dmsmccann/triton-540/spice/studies/80279/closed-loop-agc/figures/80279-full-rf-agc-attack.png

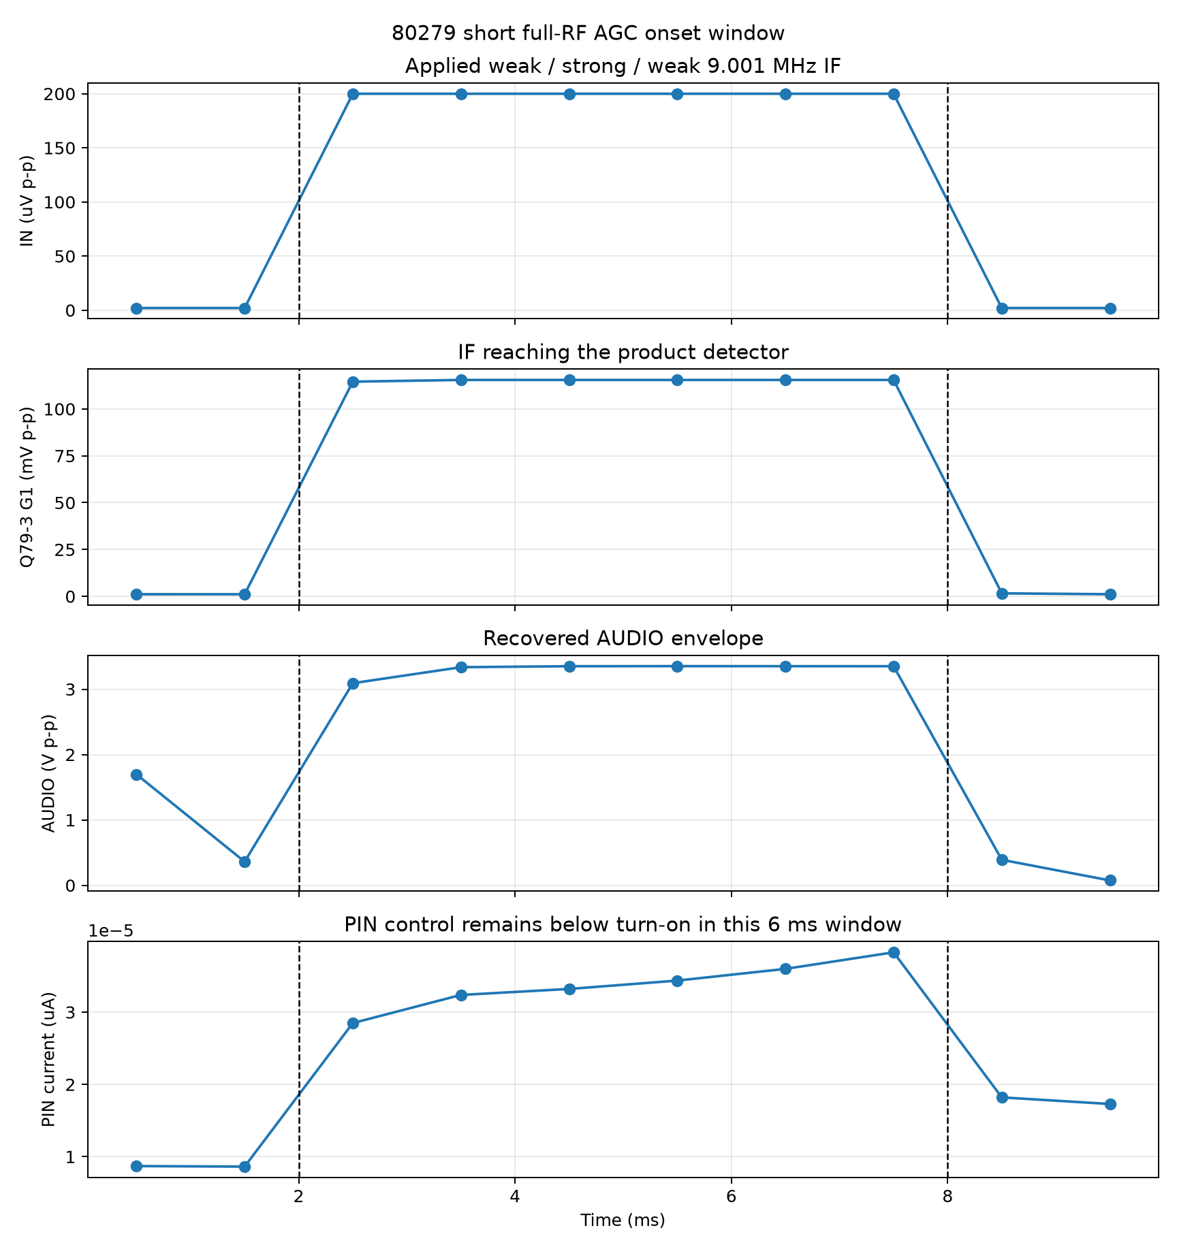
spice/studies/80279/closed-loop-agc/figures/80279-full-rf-agc-attack.png
