dmsmccann/triton-540/spice/studies/80166/manual-alignment/data/final/29p0_saved-schematic-validation.csv

frequency | user0 (gain) | user3 (gain)
28970000.0 | 71.26063842635646 | 39.748845762307894
28970444.70934756 | 71.27956110949187 | 39.75944934947092
28970889.42552171 | 71.29823011865204 | 39.76979173254958
28971334.14852256 | 71.31664334363214 | 39.779870788589776
28971778.87835021 | 71.33479870270592 | 39.789684423269634
28972223.61500477 | 71.3526941439815 | 39.79923057171336
28972668.35848634 | 71.3703276625861 | 39.808507216010966
28973113.10879503 | 71.38769728793825 | 39.81751237291327
28973557.86593094 | 71.40480109264368 | 39.826244102123084
28974002.62989417 | 71.42163719953496 | 39.834700513735925
28974447.40068484 | 71.4382037585815 | 39.84287974439121
28974892.17830305 | 71.45449897340933 | 39.85077998491168
28975336.9627489 | 71.47052108866878 | 39.858399467109926
28975781.75402249 | 71.48626840090347 | 39.865736474129626
28976226.55212393 | 71.50173925256661 | 39.87278933568876
28976671.35705333 | 71.51693202979676 | 39.87955642448672
28977116.16881079 | 71.53184517581325 | 39.88603617075028
28977560.98739642 | 71.54647717821462 | 39.89222704893736
28978005.81281031 | 71.56082657508746 | 39.89812758428635
28978450.64505258 | 71.57489196675368 | 39.903736363170175
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
