dmsmccann/triton-540/spice/studies/80289/signal-walk/data/80289-vfo-80m-signal-walk-measurements.csv

trace | mean_v | minimum_v | maximum_v | peak_to_peak_v | dominant_frequency_hz | component_2.25mhz_vpp | component_5.25mhz_vpp | component_7.5mhz_vpp | component_12.75mhz_vpp
pto_emitter_v | 1.6999995103719476 | 1.400000068162442 | 1.999999931837529 | 0.599999863675087 | 5249737.513112833 | 1.9583204355397362e-06 | 0.5999999999999996 | 1.95836131415542e-06 | 1.9584461486022534e-06
crystal_q89_3_drain_v | 7.744778808784965 | 7.742017280589295 | 7.747588980160948 | 0.00557169957165371 | 7499625.018732619 | 2.097939089247529e-06 | 7.575498280821965e-07 | 0.005557396366243375 | 6.504599511085788e-07
u89_1_pin1_v | 6.787216149807024 | 6.659375419694097 | 6.914867084712115 | 0.2554916650180177 | 5249737.513112833 | 2.480746723781994e-05 | 0.2552959477927164 | 4.365470808401273e-05 | 1.3487083771736018e-05
u89_1_pin4_v | 6.783145997120302 | 6.782941030756546 | 6.783341226276571 | 0.00040019552002501513 | 7499625.018732619 | 6.6934227813603936e-06 | 0.0001793814597817073 | 0.0002103364941931809 | 3.960542510357234e-07
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
