dmsmccann/triton-540/80166_rf_amp.kicad_sch

## KiCad design 80166_rf_amp.kicad_sch (2026-08-30, an earlier design)

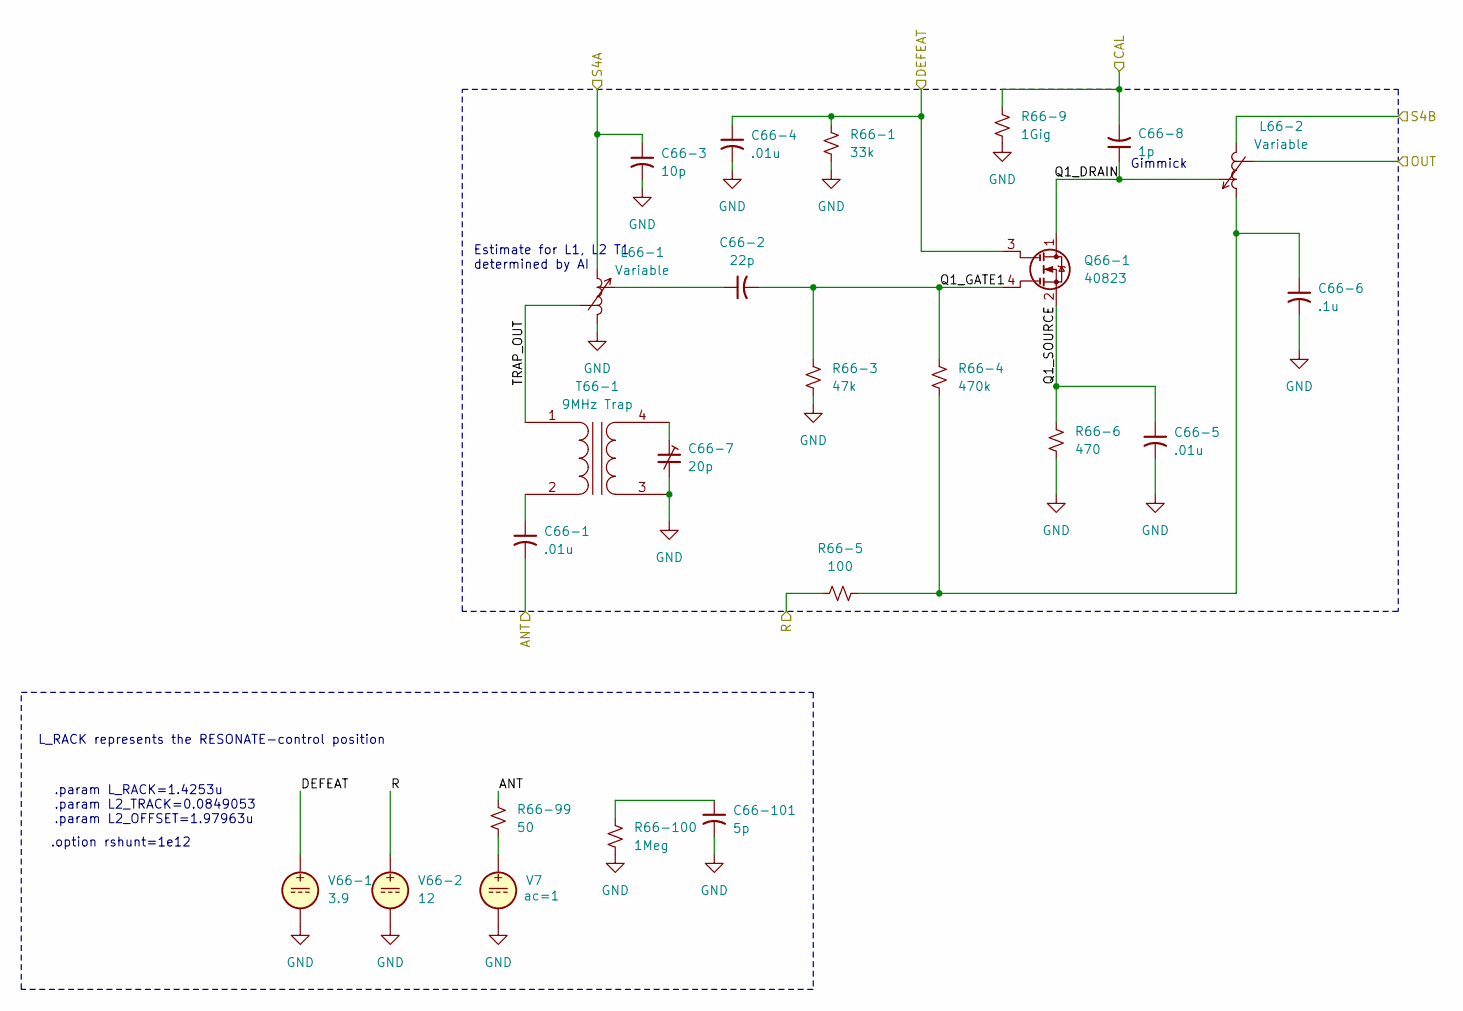
[picture p42: schematic 80166_rf_amp.kicad_sch]

Parts:
C66-1, C66-4, C66-5: .01u
C66-2: 22p
C66-3: 10p
C66-6: .1u
C66-7: 20p
C66-8: 1p
C66-101: 5p
L66-1, L66-2: Variable
Q66-1: 40823; TO-72-4
R66-1: 33k
R66-3: 47k
R66-4: 470k
R66-5: 100
R66-6: 470
R66-9: 1Gig
R66-99: 50
R66-100: 1Meg
T66-1: 9MHz Trap
V7: 0
V66-1: 3.9
V66-2: 12

Connections:
ANT: C66-1.2, R66-99.2
CAL: C66-8.2, R66-9.2
DEFEAT: C66-4.1, Q66-1.3 (G1), R66-1.2, V66-1.1
GND: C66-3.2, C66-4.2, C66-5.2, C66-6.2, C66-7.2, C66-101.2, L66-1.2, R66-1.1, R66-3.1, R66-6.1, R66-9.1, R66-100.1, T66-1.3 (SA), V7.2, V66-1.2, V66-2.2
unnamed: C66-1.1, T66-1.2 (AB)
unnamed: C66-2.1, L66-1.4
unnamed: C66-6.1, L66-2.1, R66-4.1, R66-5.2
unnamed: C66-7.1, T66-1.4 (SB)
unnamed: C66-101.1, R66-100.2
unnamed: R66-99.1, V7.1
OUT: L66-2.3
Q1_DRAIN: C66-8.1, L66-2.4, Q66-1.1 (D)
Q1_GATE1: C66-2.2, Q66-1.4 (S), R66-3.2, R66-4.2
Q1_SOURCE: C66-5.1, Q66-1.2 (G2), R66-6.2
R: R66-5.1, V66-2.1
S4A: C66-3.1, L66-1.1
S4B: L66-2.2
TRAP_OUT: L66-1.3, T66-1.1 (AA)

Notes on the sheet:
.param L_RACK=1.4253u .param L2_TRACK=0.0849053 .param L2_OFFSET=1.97963u
Gimmick
L_RACK represents the RESONATE-control position
.option rshunt=1e12
Estimate for L1, L2 T1 determined by AI
