dmsmccann/triton-540/80274_audio_power_amp.kicad_sch

## KiCad design 80274_audio_power_amp.kicad_sch (2026-09-05)

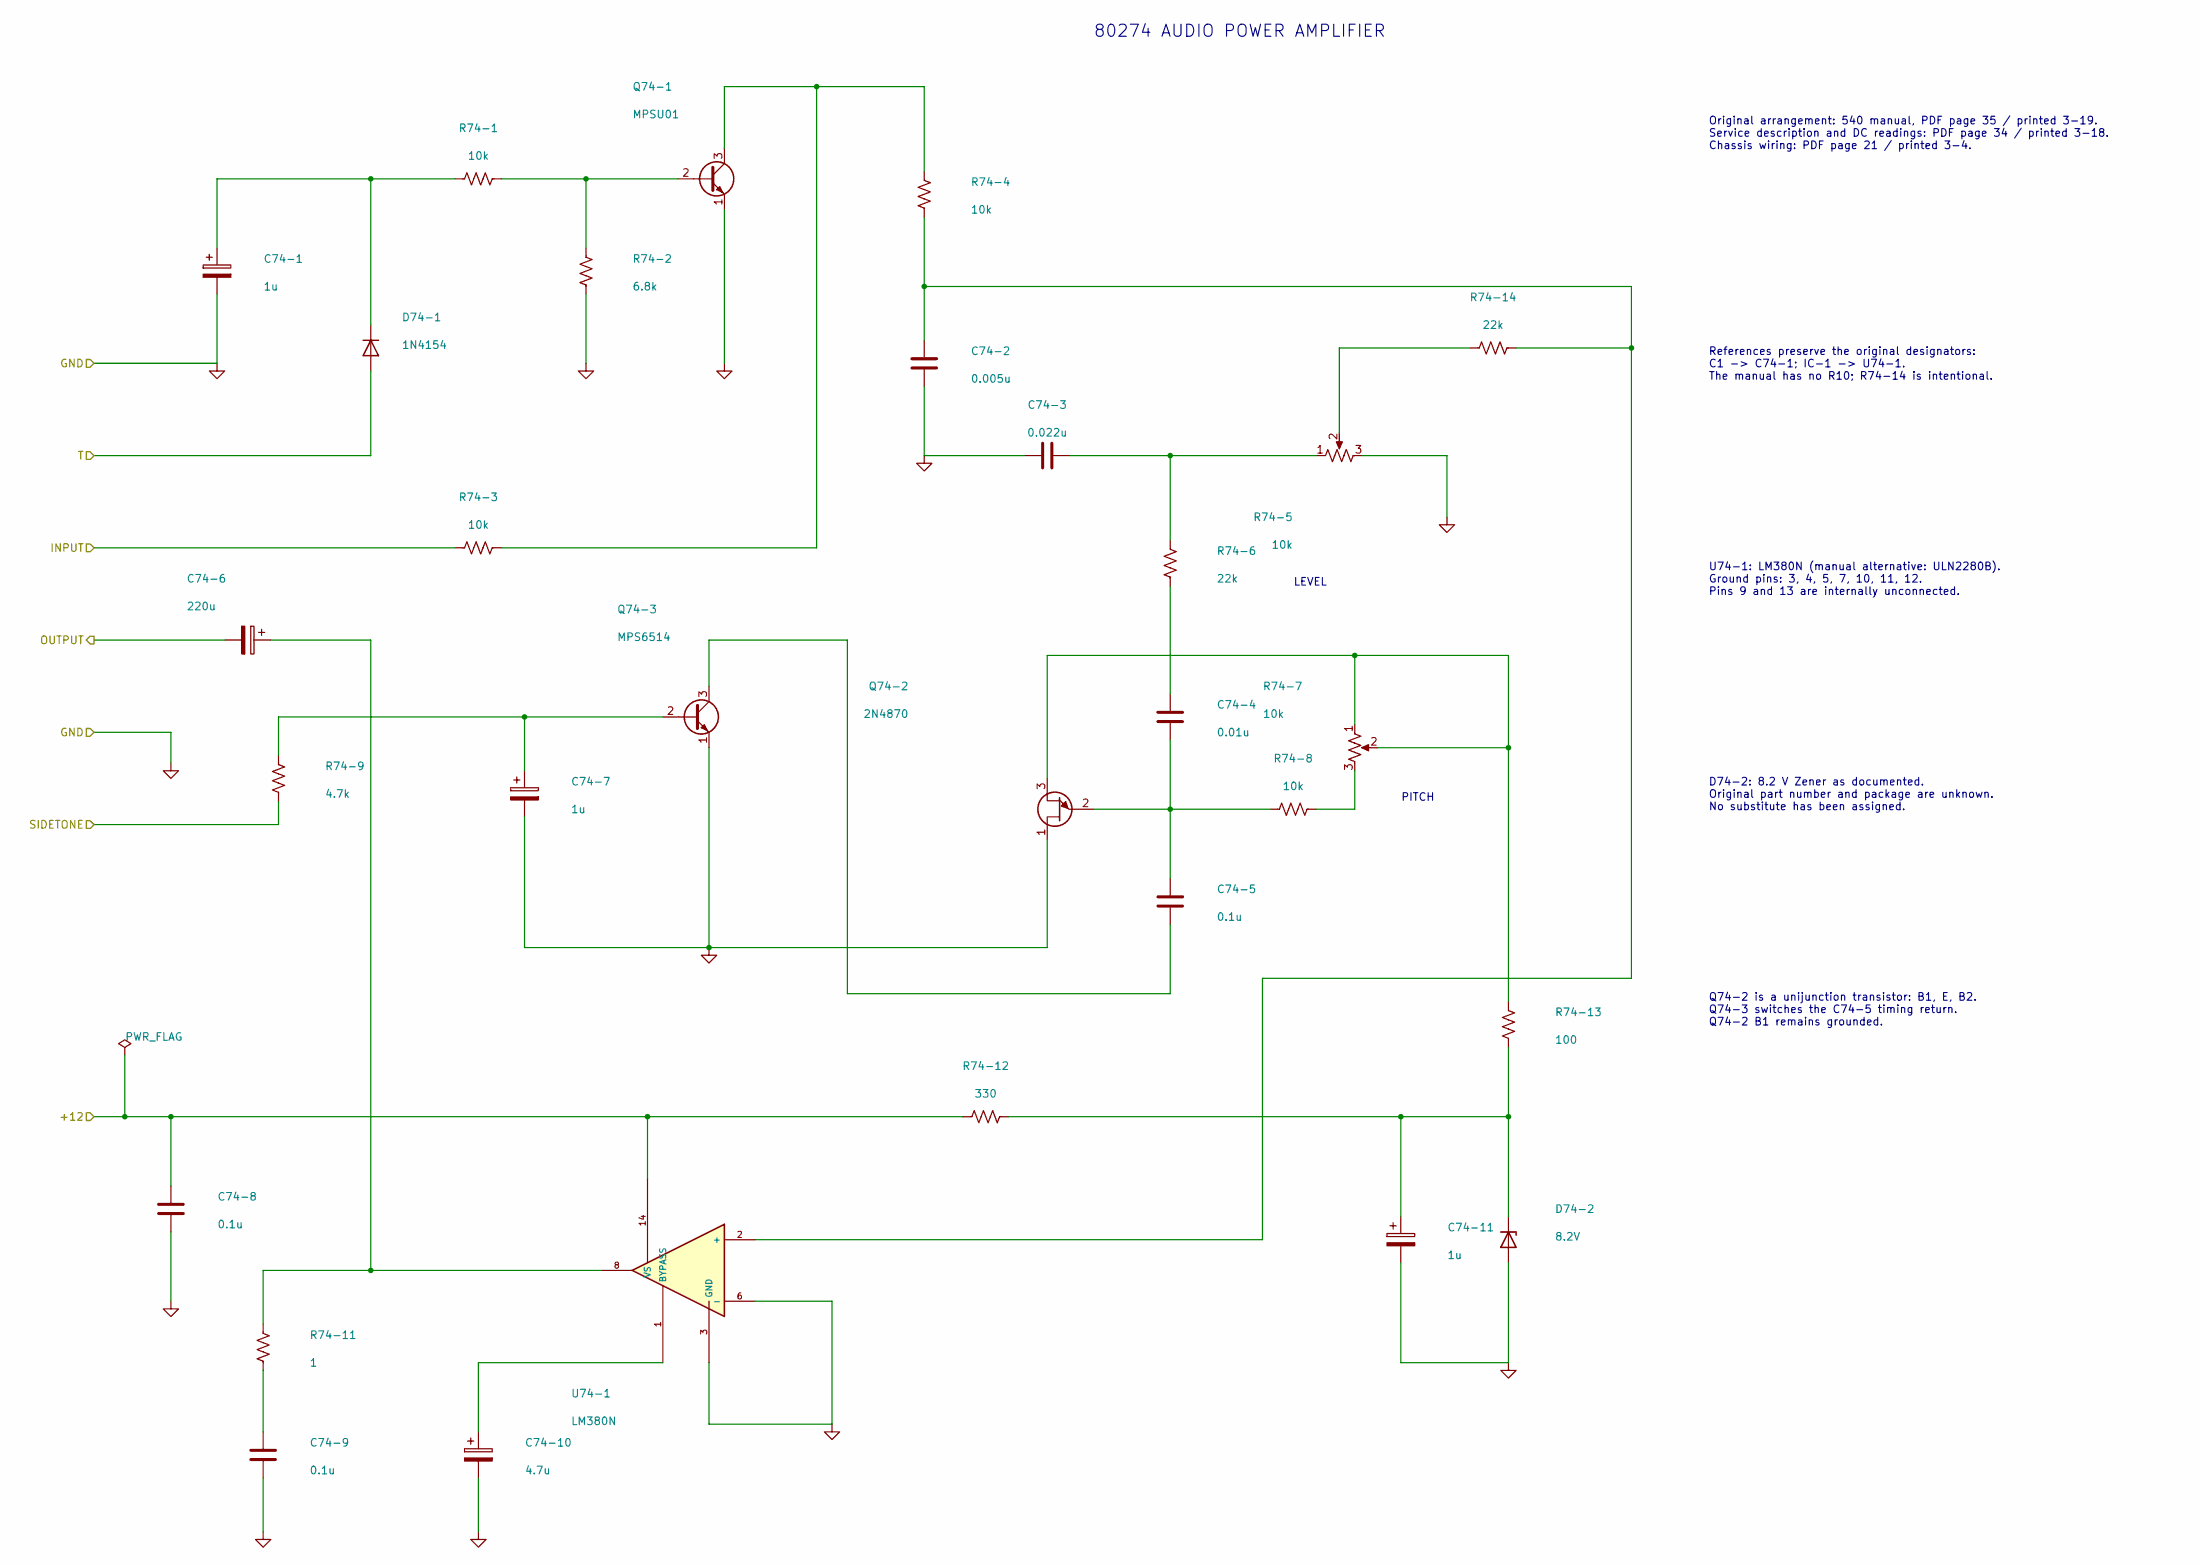
[picture p43: schematic 80274_audio_power_amp.kicad_sch]

Parts:
C74-1, C74-7, C74-11: 1u
C74-2: 0.005u
C74-3: 0.022u
C74-4: 0.01u
C74-5, C74-8, C74-9: 0.1u
C74-6: 220u
C74-10: 4.7u
D74-1: 1N4154
D74-2: 8.2V
Q74-1: MPSU01
Q74-2: 2N4870
Q74-3: MPS6514
R74-1, R74-3, R74-4, R74-5, R74-7, R74-8: 10k
R74-2: 6.8k
R74-6, R74-14: 22k
R74-9: 4.7k
R74-11: 1
R74-12: 330
R74-13: 100
U74-1: LM380N; DIP-14_W7.62mm

Connections:
+12: C74-8.1, R74-12.2, U74-1.14 (VS)
GND: C74-1.2, C74-2.2, C74-3.2, C74-7.2, C74-8.2, C74-9.2, C74-10.2, C74-11.2, D74-2.2 (A), Q74-1.1 (E), Q74-2.1 (B1), Q74-3.1 (E), R74-2.2, R74-5.3, U74-1.3 (GND), U74-1.4 (GND), U74-1.5 (GND), U74-1.6 (-), U74-1.7 (GND), U74-1.10 (GND), U74-1.11 (GND), U74-1.12 (GND)
INPUT: R74-3.2
unnamed: C74-1.1, D74-1.1 (K), R74-1.2
unnamed: C74-2.1, R74-4.2, R74-14.1, U74-1.2 (+)
unnamed: C74-3.1, R74-5.1, R74-6.1
unnamed: C74-4.1, R74-6.2
unnamed: C74-4.2, C74-5.1, Q74-2.2 (E), R74-8.2
unnamed: C74-5.2, Q74-3.3 (C)
unnamed: C74-6.1, R74-11.1, U74-1.8
unnamed: C74-7.1, Q74-3.2 (B), R74-9.1
unnamed: C74-9.1, R74-11.2
unnamed: C74-10.1, U74-1.1 (BYPASS)
unnamed: C74-11.1, D74-2.1 (K), R74-12.1, R74-13.2
unnamed: Q74-1.2 (B), R74-1.1, R74-2.1
unnamed: Q74-1.3 (C), R74-3.1, R74-4.1
unnamed: Q74-2.3 (B2), R74-7.1, R74-7.2, R74-13.1
unnamed: R74-7.3, R74-8.1
unnamed: R74-5.2, R74-14.2
OUTPUT: C74-6.2
SIDETONE: R74-9.2
T: D74-1.2 (A)

Notes on the sheet:
LEVEL
PITCH
80274 AUDIO POWER AMPLIFIER
Original arrangement: 540 manual, PDF page 35 / printed 3-19. Service description and DC readings: PDF page 34 / printed 3-18. Chassis wiring: PDF page 21 / printed 3-4.
References preserve the original designators: C1 -> C74-1; IC-1 -> U74-1. The manual has no R10; R74-14 is intentional.
U74-1: LM380N (manual alternative: ULN2280B). Ground pins: 3, 4, 5, 7, 10, 11, 12. Pins 9 and 13 are internally unconnected.
D74-2: 8.2 V Zener as documented. Original part number and package are unknown. No substitute has been assigned.
Q74-2 is a unijunction transistor: B1, E, B2. Q74-3 switches the C74-5 timing return. Q74-2 B1 remains grounded.
