dmsmccann/triton-540/80279_if_agc.kicad_sch

## KiCad design 80279_if_agc.kicad_sch (2026-08-18)

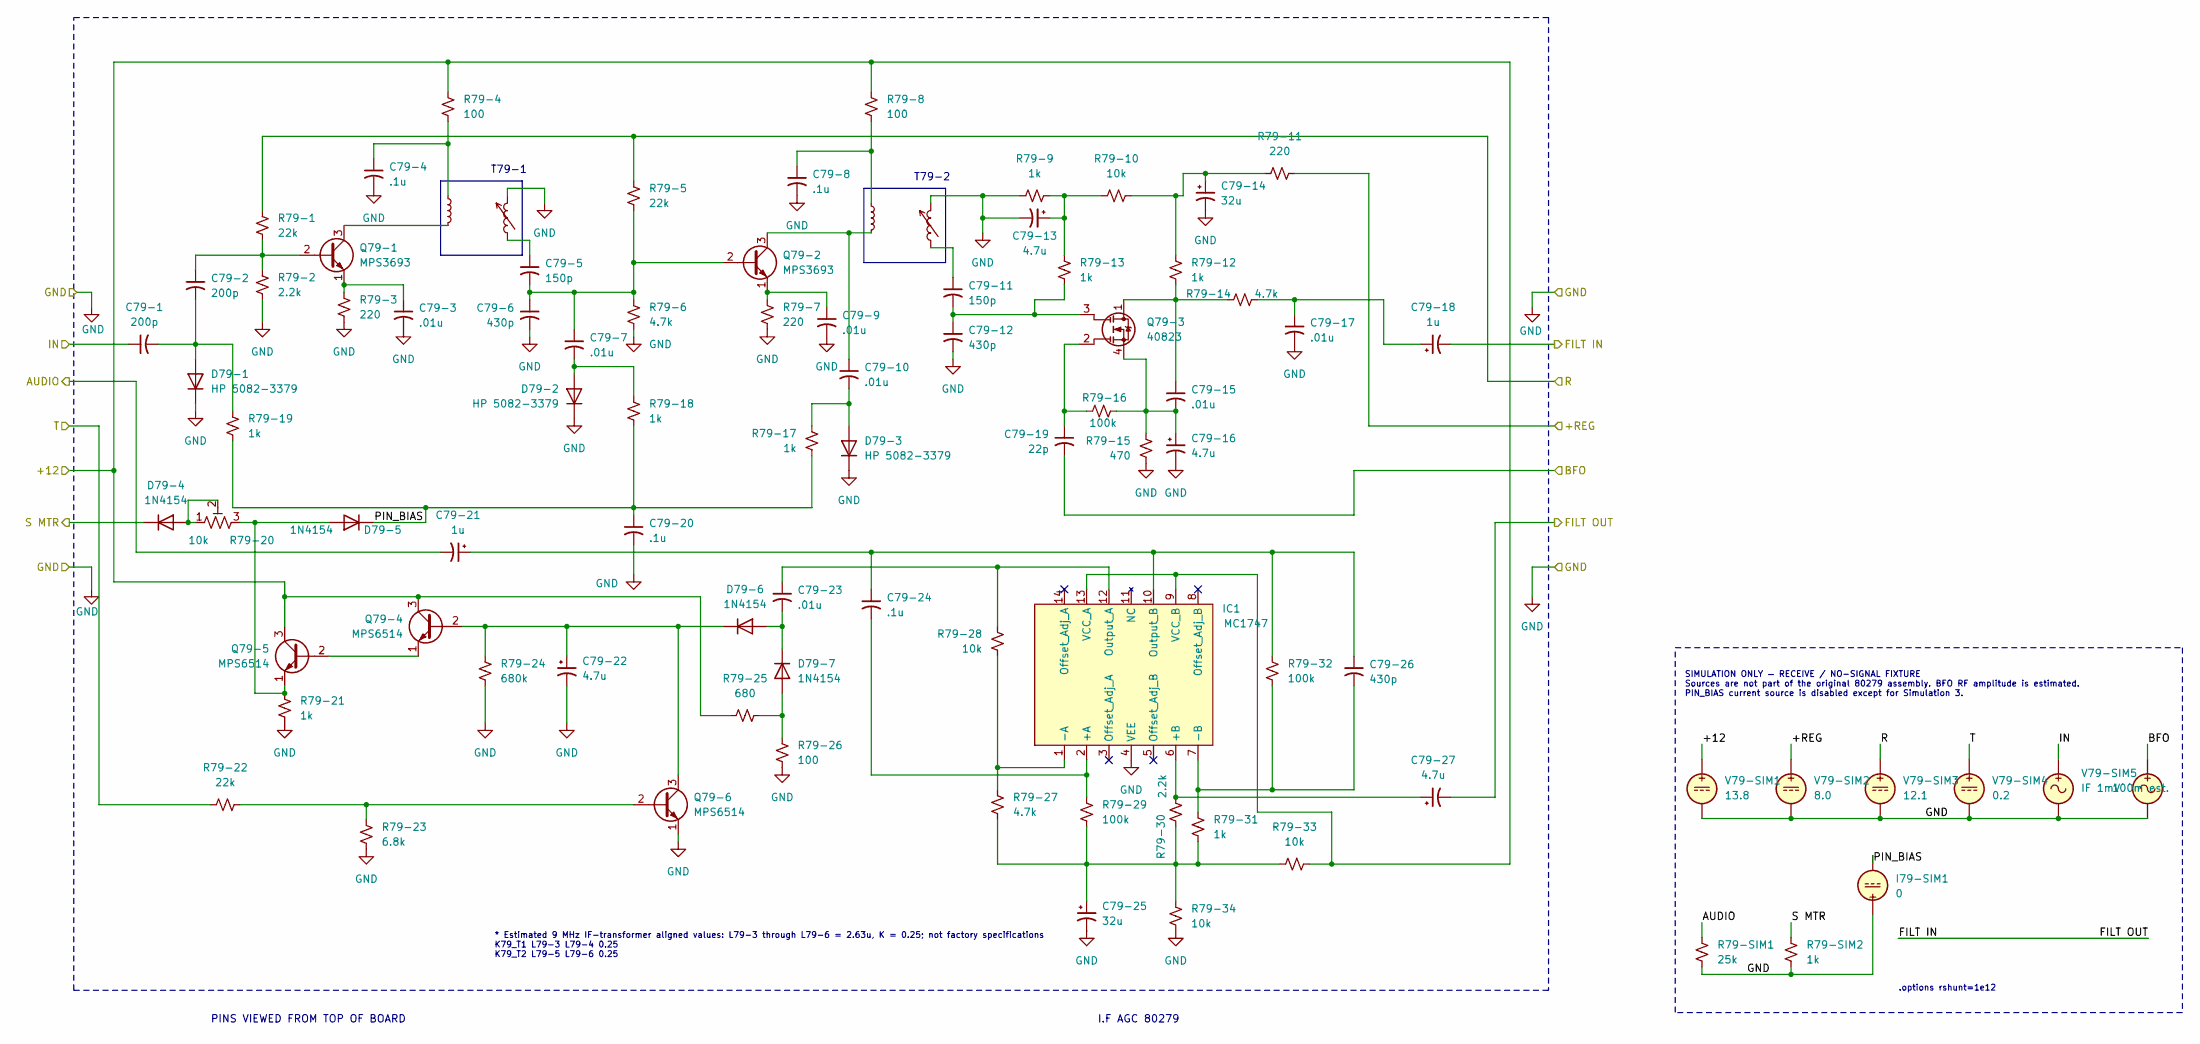
[picture p44: schematic 80279_if_agc.kicad_sch]

Parts:
C79-1, C79-2: 200p
C79-3, C79-7, C79-9, C79-10, C79-15, C79-17, C79-23: .01u
C79-4, C79-8, C79-20, C79-24: .1u
C79-5, C79-11: 150p
C79-6, C79-12, C79-26: 430p
C79-13, C79-16, C79-22, C79-27: 4.7u
C79-14, C79-25: 32u
C79-18, C79-21: 1u
C79-19: 22p
D79-1, D79-2, D79-3: HP 5082-3379
D79-4, D79-5, D79-6, D79-7: 1N4154
I79-SIM1: 0
IC1: MC1747
L79-3, L79-4, L79-5, L79-6: 2.63u
Q79-1, Q79-2: MPS3693
Q79-3: 40823; TO-72-4
Q79-4, Q79-5, Q79-6: MPS6514
R79-1, R79-5, R79-22: 22k
R79-2, R79-30: 2.2k
R79-3, R79-7, R79-11: 220
R79-4, R79-8, R79-26: 100
R79-6, R79-14, R79-27: 4.7k
R79-9, R79-12, R79-13, R79-17, R79-18, R79-19, R79-21, R79-31, R79-SIM2: 1k
R79-10, R79-20, R79-28, R79-33, R79-34: 10k
R79-15: 470
R79-16, R79-29, R79-32: 100k
R79-23: 6.8k
R79-24: 680k
R79-25: 680
R79-SIM1: 25k
V79-SIM1: 13.8
V79-SIM2: 8.0
V79-SIM3: 12.1
V79-SIM4: 0.2
V79-SIM5: IF 1mV
V79-SIM6: 100m est.

Connections:
+12: IC1.9 (VCC_B), IC1.13 (VCC_A), Q79-4.3 (C), Q79-5.3 (C), R79-4.1, R79-8.1, R79-25.1, R79-33.2, V79-SIM1.1
+REG: R79-11.2, V79-SIM2.1
AUDIO: C79-21.2, R79-SIM1.1
BFO: C79-19.2, V79-SIM6.1
FILT IN: C79-18.2
FILT OUT: C79-27.2
GND: C79-3.2, C79-4.2, C79-6.2, C79-8.2, C79-9.2, C79-12.2, C79-13.2, C79-14.2, C79-16.2, C79-17.2, C79-20.2, C79-22.2, C79-25.2, D79-1.1 (K), D79-2.1 (K), D79-3.1 (K), I79-SIM1.1, IC1.4 (VEE), L79-4.1, L79-6.1, Q79-6.1 (E), R79-2.2, R79-3.2, R79-6.2, R79-7.2, R79-9.1, R79-15.2, R79-21.2, R79-23.2, R79-24.2, R79-26.2, R79-34.2, R79-SIM1.2, R79-SIM2.2, V79-SIM1.2, V79-SIM2.2, V79-SIM3.2, V79-SIM4.2, V79-SIM5.2, V79-SIM6.2
IN: C79-1.1, V79-SIM5.1
unnamed: C79-1.2, C79-2.2, D79-1.2 (A), R79-19.1
unnamed: C79-2.1, Q79-1.2 (B), R79-1.2, R79-2.1
unnamed: C79-3.1, Q79-1.1 (E), R79-3.1
unnamed: C79-4.1, L79-3.1, R79-4.2
unnamed: C79-5.1, L79-4.2
unnamed: C79-5.2, C79-6.1, C79-7.1, Q79-2.2 (B), R79-5.2, R79-6.1
unnamed: C79-7.2, D79-2.2 (A), R79-18.1
unnamed: C79-8.1, L79-5.1, R79-8.2
unnamed: C79-9.1, Q79-2.1 (E), R79-7.1
unnamed: C79-10.1, L79-5.2, Q79-2.3 (C)
unnamed: C79-10.2, D79-3.2 (A), R79-17.1
unnamed: C79-11.1, L79-6.2
unnamed: C79-11.2, C79-12.1, Q79-3.3 (G1), R79-13.2
unnamed: C79-13.1, R79-9.2, R79-10.1, R79-13.1
unnamed: C79-14.1, R79-10.2, R79-11.1, R79-12.1
unnamed: C79-15.1, Q79-3.1 (D), R79-12.2, R79-14.1
unnamed: C79-15.2, C79-16.1, Q79-3.4 (S), R79-15.1, R79-16.2
unnamed: C79-17.1, C79-18.1, R79-14.2
unnamed: C79-19.1, Q79-3.2 (G2), R79-16.1
unnamed: C79-21.1, C79-24.1, C79-26.1, IC1.10 (Output_B), R79-32.1
unnamed: C79-22.1, D79-6.1 (K), Q79-4.2 (B), Q79-6.3 (C), R79-24.1
unnamed: C79-23.1, IC1.12 (Output_A), R79-28.1
unnamed: C79-23.2, D79-6.2 (A), D79-7.1 (K)
unnamed: C79-24.2, IC1.2 (+A), R79-29.1
unnamed: C79-25.1, R79-27.2, R79-29.2, R79-30.2, R79-31.2, R79-33.1, R79-34.1
unnamed: C79-26.2, IC1.7 (-B), R79-31.1, R79-32.2
unnamed: C79-27.1, IC1.6 (+B), R79-30.1
unnamed: D79-4.2 (A), R79-20.1, R79-20.2
unnamed: D79-5.2 (A), Q79-5.1 (E), R79-20.3, R79-21.1
unnamed: D79-7.2 (A), R79-25.2, R79-26.1
unnamed: IC1.1 (-A), R79-27.1, R79-28.2
unnamed: L79-3.2, Q79-1.3 (C)
unnamed: Q79-4.1 (E), Q79-5.2 (B)
unnamed: Q79-6.2 (B), R79-22.2, R79-23.1
PIN_BIAS: C79-20.1, D79-5.1 (K), I79-SIM1.2, R79-17.2, R79-18.2, R79-19.2
R: R79-1.1, R79-5.1, V79-SIM3.1
S MTR: D79-4.1 (K), R79-SIM2.1
T: R79-22.1, V79-SIM4.1

Notes on the sheet:
PINS VIEWED FROM TOP OF BOARD
I.F AGC 80279
T79-1
T79-2
SIMULATION ONLY — RECEIVE / NO-SIGNAL FIXTURE Sources are not part of the original 80279 assembly. BFO RF amplitude is estimated. PIN_BIAS current source is disabled except for Simulation 3.
* Estimated 9 MHz IF-transformer aligned values: L79-3 through L79-6 = 2.63u, K = 0.25; not factory specifications K79_T1 L79-3 L79-4 0.25 K79_T2 L79-5 L79-6 0.25
.options rshunt=1e12
