dmsmccann/triton-540/80287_tx_rx_mixer.kicad_sch

## KiCad design 80287_tx_rx_mixer.kicad_sch (2026-08-17)

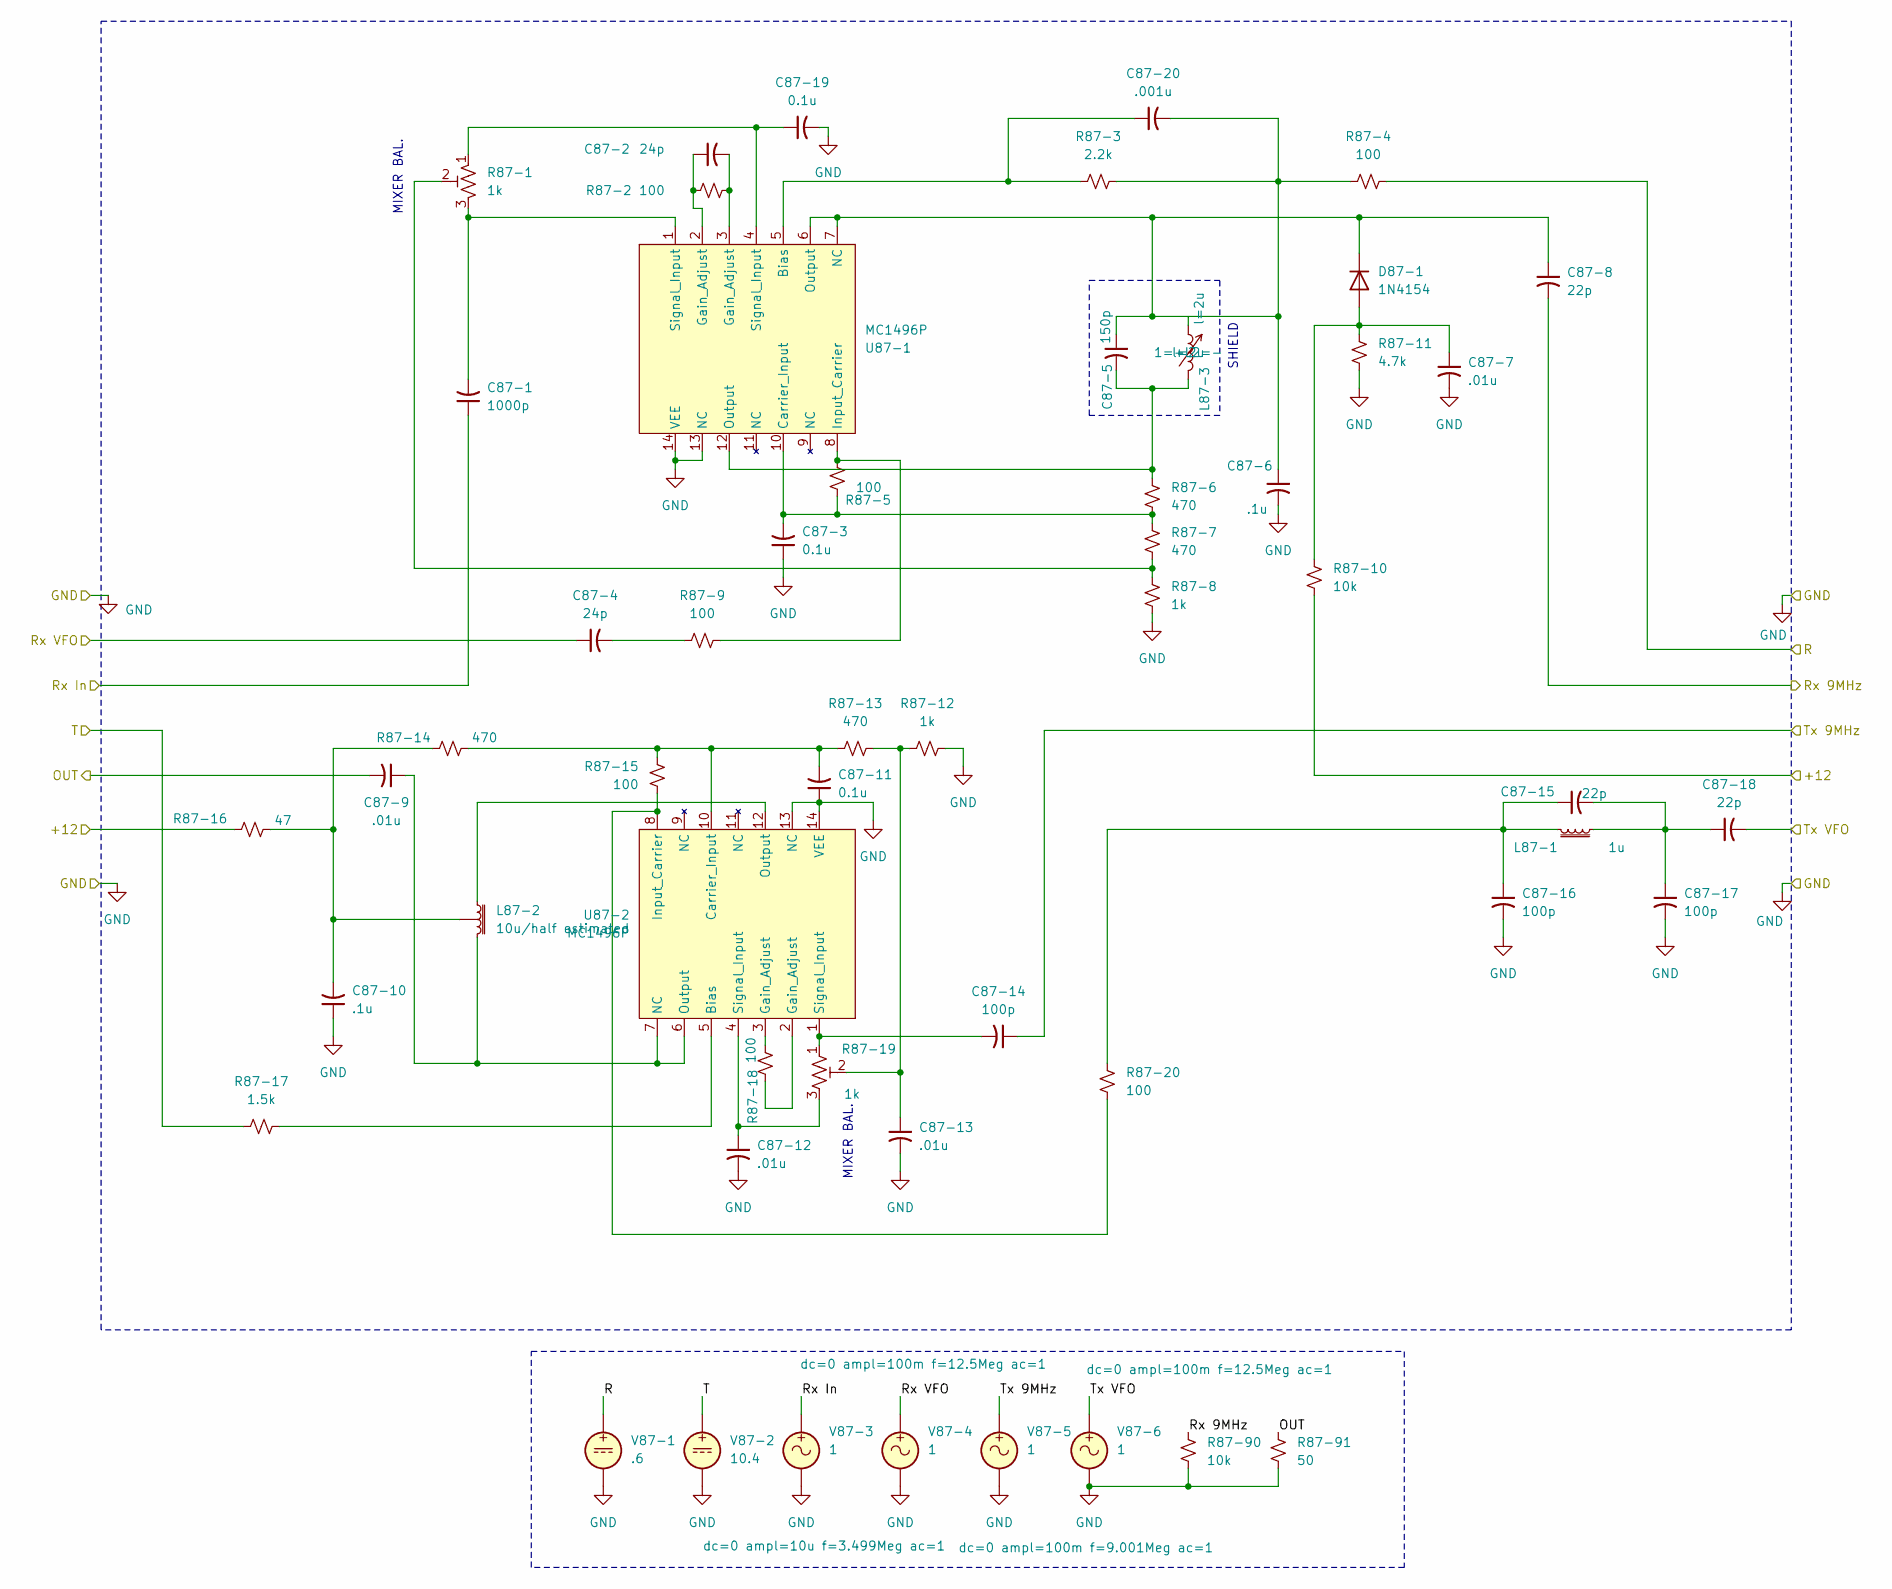
[picture p45: schematic 80287_tx_rx_mixer.kicad_sch]

Parts:
C87-1: 1000p
C87-2, C87-4: 24p
C87-3, C87-11, C87-19: 0.1u
C87-5: 150p
C87-6, C87-10: .1u
C87-7, C87-9, C87-12, C87-13: .01u
C87-8, C87-15, C87-18: 22p
C87-14, C87-16, C87-17: 100p
C87-20: .001u
D87-1: 1N4154
L87-1: 1u
L87-2: 10u/half estimated
L87-3: l=2u
R87-1, R87-8, R87-12, R87-19: 1k
R87-2, R87-4, R87-5, R87-9, R87-15, R87-18, R87-20: 100
R87-3: 2.2k
R87-6, R87-7, R87-13, R87-14: 470
R87-10, R87-90: 10k
R87-11: 4.7k
R87-16: 47
R87-17: 1.5k
R87-91: 50
U87-1, U87-2: MC1496P
V87-1: .6
V87-2: 10.4
V87-3, V87-4, V87-5, V87-6: 1

Connections:
+12: R87-10.1, R87-16.2
GND: C87-3.1, C87-6.2, C87-7.2, C87-10.1, C87-11.1, C87-12.2, C87-13.2, C87-16.2, C87-17.2, C87-19.2, R87-8.1, R87-11.1, R87-12.1, R87-90.2, R87-91.2, U87-1.13 (NC), U87-1.14 (VEE), U87-2.13 (NC), U87-2.14 (VEE), V87-1.2, V87-2.2, V87-3.2, V87-4.2, V87-5.2, V87-6.2
unnamed: C87-1.2, R87-1.3, U87-1.1 (Signal_Input)
unnamed: C87-2.1, R87-2.1, U87-1.2 (Gain_Adjust)
unnamed: C87-2.2, R87-2.2, U87-1.3 (Gain_Adjust)
unnamed: C87-3.2, R87-5.1, R87-6.1, R87-7.2, U87-1.10 (Carrier_Input)
unnamed: C87-4.2, R87-9.2
unnamed: C87-5.2, L87-3.2, R87-6.2, U87-1.12 (Output)
unnamed: C87-7.1, D87-1.2 (A), R87-10.2, R87-11.2
unnamed: C87-9.1, L87-2.2, U87-2.6 (Output), U87-2.7 (NC)
unnamed: C87-10.2, L87-2.3, R87-14.2, R87-16.1
unnamed: C87-11.2, R87-13.2, R87-14.1, R87-15.2, U87-2.10 (Carrier_Input)
unnamed: C87-12.1, R87-19.3, U87-2.4 (Signal_Input)
unnamed: C87-13.1, R87-12.2, R87-13.1, R87-19.2
unnamed: C87-14.2, R87-19.1, U87-2.1 (Signal_Input)
unnamed: C87-15.1, C87-16.1, L87-1.2, R87-20.1
unnamed: C87-15.2, C87-17.1, C87-18.1, L87-1.1
unnamed: C87-19.1, R87-1.1, U87-1.4 (Signal_Input)
unnamed: C87-20.1, R87-3.2, U87-1.5 (Bias)
unnamed: C87-5.1, C87-6.1, C87-8.1, C87-20.2, D87-1.1 (K), L87-3.1, R87-3.1, R87-4.2, U87-1.6 (Output), U87-1.7 (NC)
unnamed: L87-2.1, U87-2.12 (Output)
unnamed: R87-1.2, R87-7.1, R87-8.2
unnamed: R87-5.2, R87-9.1, U87-1.8 (Input_Carrier)
unnamed: R87-15.1, R87-20.2, U87-2.8 (Input_Carrier)
unnamed: R87-17.1, U87-2.5 (Bias)
unnamed: R87-18.1, U87-2.2 (Gain_Adjust)
unnamed: R87-18.2, U87-2.3 (Gain_Adjust)
OUT: C87-9.2, R87-91.1
R: R87-4.1, V87-1.1
Rx 9MHz: C87-8.2, R87-90.1
Rx In: C87-1.1, V87-3.1
Rx VFO: C87-4.1, V87-4.1
T: R87-17.2, V87-2.1
Tx 9MHz: C87-14.1, V87-5.1
Tx VFO: C87-18.2, V87-6.1

Notes on the sheet:
MIXER BAL.
SHIELD
