dmsmccann/triton-540/80289_vfo.kicad_sch

## KiCad design 80289_vfo.kicad_sch (2026-08-17)

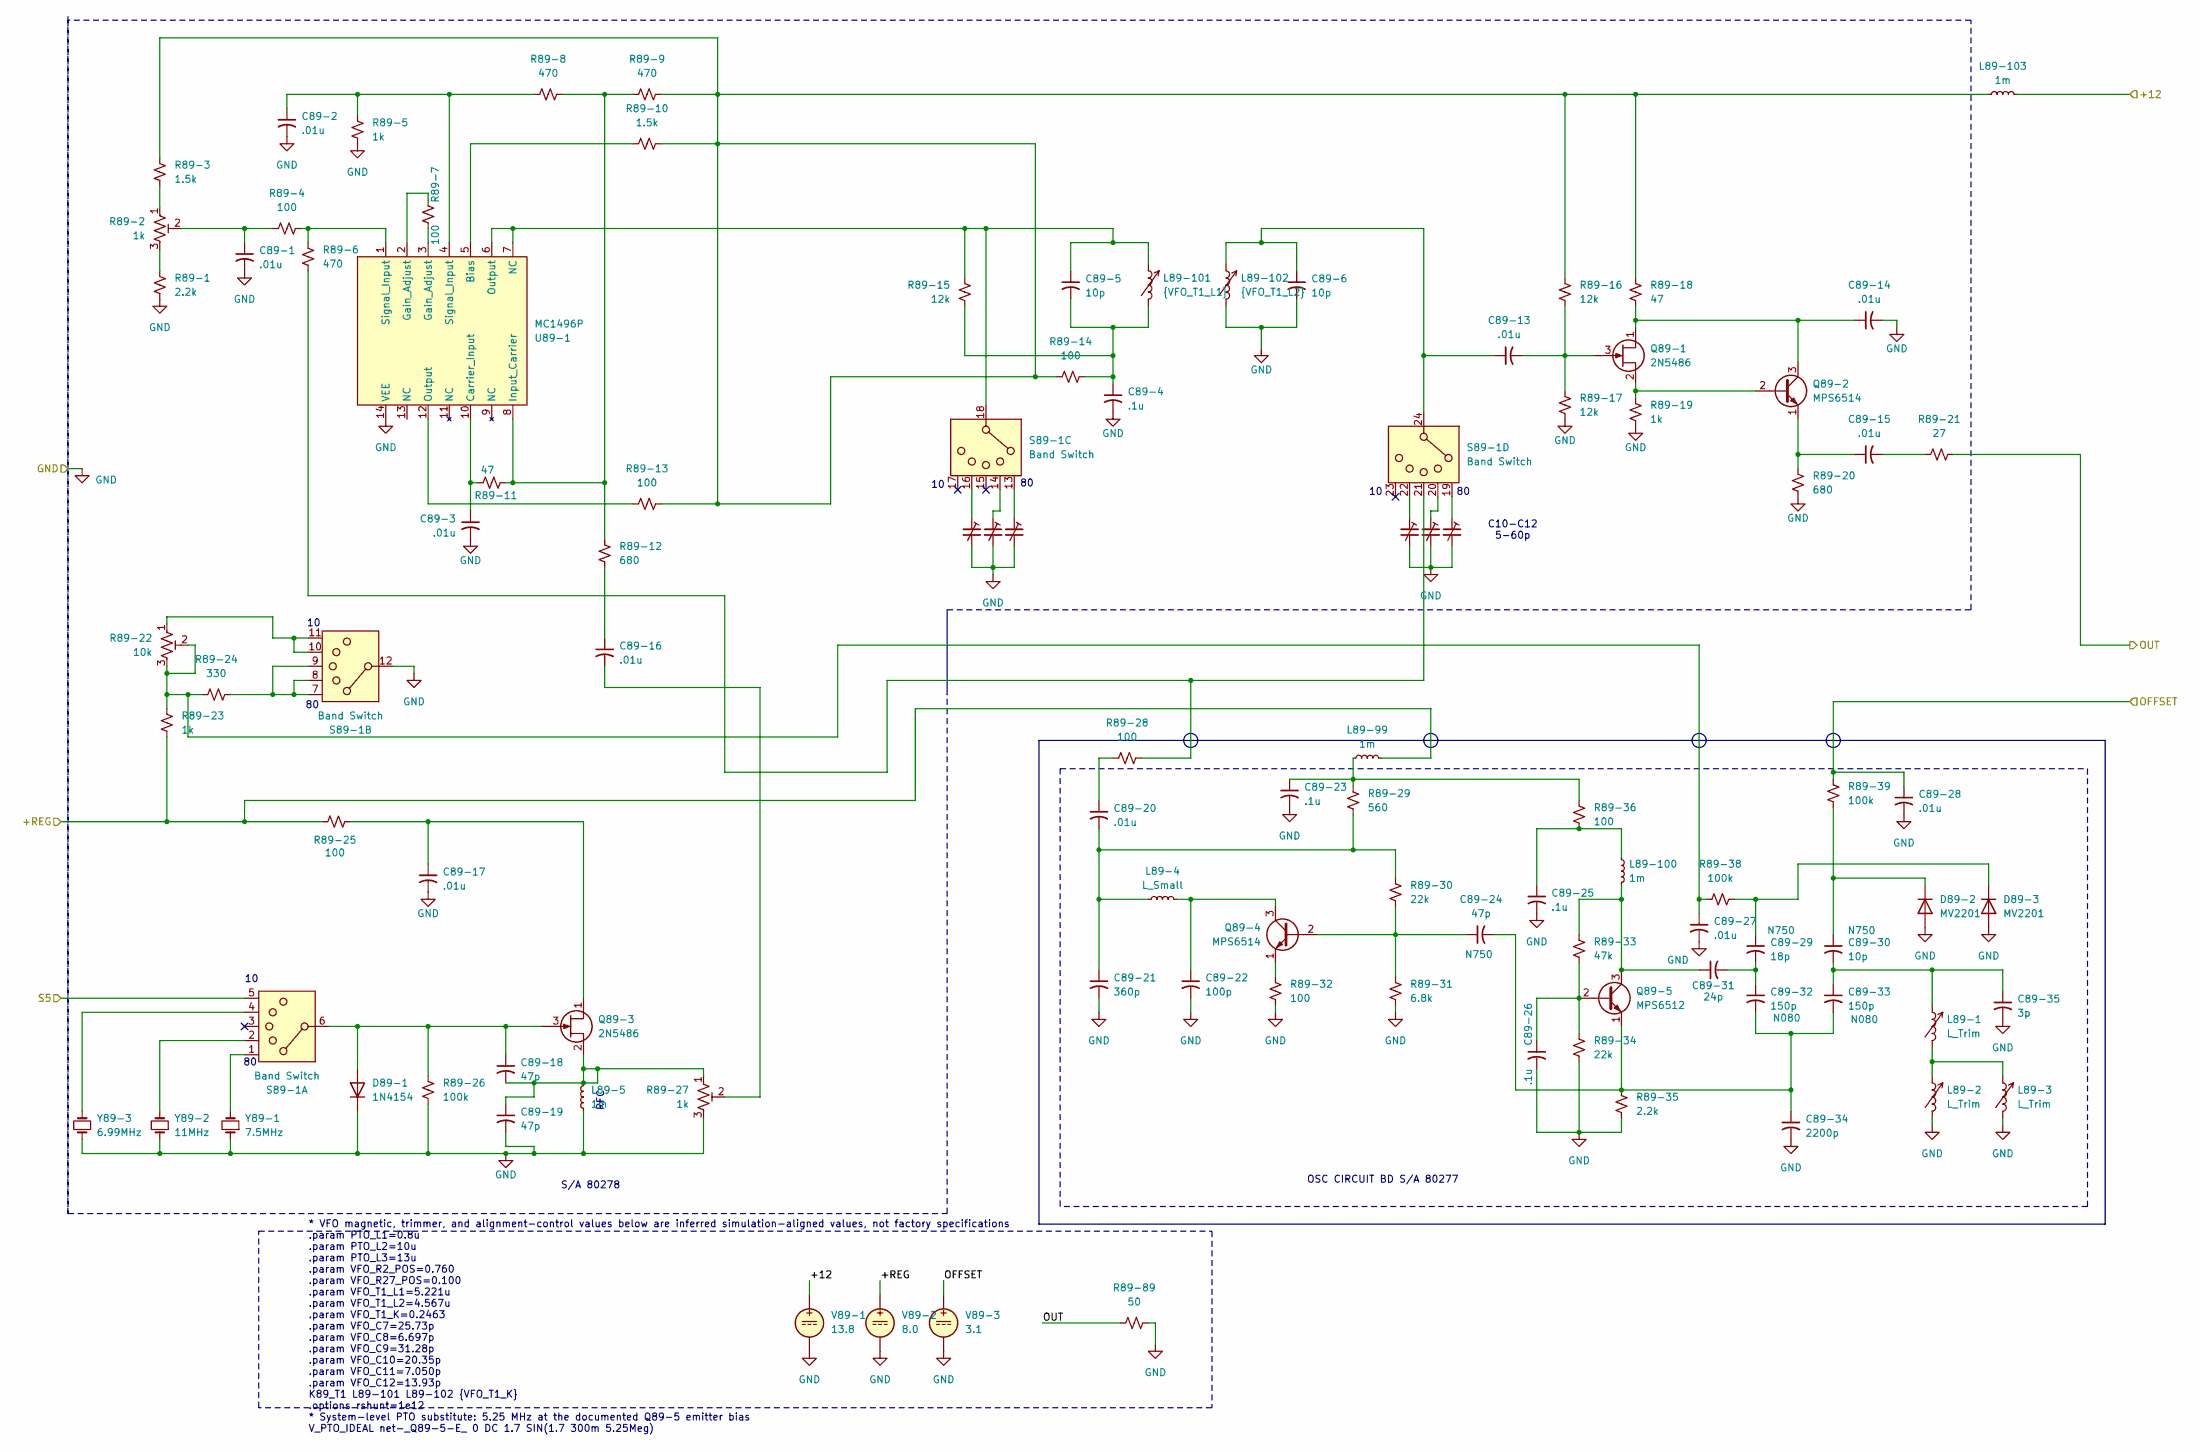
[picture p46: schematic 80289_vfo.kicad_sch]

Parts:
C89-1, C89-2, C89-3, C89-13, C89-14, C89-15, C89-16, C89-17, C89-20, C89-27, C89-28: .01u
C89-4, C89-23, C89-25, C89-26: .1u
C89-5, C89-6, C89-30: 10p
C89-7: {VFO_C7}
C89-8: {VFO_C8}
C89-9: {VFO_C9}
C89-10: {VFO_C10}
C89-11: {VFO_C11}
C89-12: {VFO_C12}
C89-18, C89-19, C89-24: 47p
C89-21: 360p
C89-22: 100p
C89-29: 18p
C89-31: 24p
C89-32, C89-33: 150p
C89-34: 2200p
C89-35: 3p
D89-1: 1N4154
D89-2, D89-3: MV2201
L89-1, L89-2, L89-3: L_Trim
L89-4: L_Small
L89-5, L89-99, L89-100, L89-103: 1m
L89-101: {VFO_T1_L1}
L89-102: {VFO_T1_L2}
Q89-1, Q89-3: 2N5486
Q89-2, Q89-4: MPS6514
Q89-5: MPS6512
R89-1, R89-35: 2.2k
R89-2, R89-5, R89-19, R89-23, R89-27: 1k
R89-3, R89-10: 1.5k
R89-4, R89-7, R89-13, R89-14, R89-25, R89-28, R89-32, R89-36: 100
R89-6, R89-8, R89-9: 470
R89-11, R89-18: 47
R89-12, R89-20: 680
R89-15, R89-16, R89-17: 12k
R89-21: 27
R89-22: 10k
R89-24: 330
R89-26, R89-38, R89-39: 100k
R89-29: 560
R89-30, R89-34: 22k
R89-31: 6.8k
R89-33: 47k
R89-89: 50
S89-1: Band Switch
U89-1: MC1496P
V89-1: 13.8
V89-2: 8.0
V89-3: 3.1
Y89-1: 7.5MHz
Y89-2: 11MHz
Y89-3: 6.99MHz

Connections:
+12: L89-103.2, V89-1.1
+REG: L89-99.2, R89-23.2, R89-25.2, V89-2.1
GND: C89-1.2, C89-2.2, C89-3.2, C89-4.2, C89-6.2, C89-7.2, C89-8.2, C89-9.2, C89-10.2, C89-11.2, C89-12.2, C89-14.2, C89-17.2, C89-19.2, C89-21.2, C89-22.2, C89-23.2, C89-25.2, C89-26.2, C89-27.2, C89-28.2, C89-34.2, C89-35.2, D89-1.1 (K), D89-2.2 (A), D89-3.2 (A), L89-2.2, L89-3.2, L89-5.1, L89-102.2, R89-1.1, R89-5.1, R89-17.2, R89-19.2, R89-20.2, R89-26.2, R89-27.3, R89-31.1, R89-32.1, R89-34.1, R89-35.1, R89-89.2, S89-1.12 (B-COM), U89-1.14 (VEE), V89-1.2, V89-2.2, V89-3.2, Y89-1.1, Y89-2.1, Y89-3.1
unnamed: C89-1.1, R89-2.2, R89-4.1
unnamed: C89-2.1, R89-5.2, R89-8.2, U89-1.4 (Signal_Input)
unnamed: C89-3.1, R89-11.2, U89-1.10 (Carrier_Input)
unnamed: C89-4.1, C89-5.2, L89-101.2, R89-14.1, R89-15.2
unnamed: C89-5.1, L89-101.1, R89-15.1, S89-1.18 (C-COM), U89-1.6 (Output), U89-1.7 (NC)
unnamed: C89-7.1, S89-1.16 (C4)
unnamed: C89-8.1, S89-1.14 (C2)
unnamed: C89-9.1, S89-1.13 (C1)
unnamed: C89-10.1, S89-1.22 (D4)
unnamed: C89-11.1, S89-1.20 (D2)
unnamed: C89-12.1, S89-1.19 (D1)
unnamed: C89-6.1, C89-13.1, L89-102.1, S89-1.24 (D-COM)
unnamed: C89-13.2, Q89-1.3 (G), R89-16.2, R89-17.1
unnamed: C89-14.1, Q89-1.1 (D), Q89-2.3 (C), R89-18.2
unnamed: C89-15.1, Q89-2.1 (E), R89-20.1
unnamed: C89-15.2, R89-21.1
unnamed: C89-16.1, R89-12.1
unnamed: C89-16.2, R89-27.2
unnamed: C89-17.1, Q89-3.1 (D), R89-25.1
unnamed: C89-18.1, D89-1.2 (A), Q89-3.3 (G), R89-26.1, S89-1.6 (A-COM)
unnamed: C89-18.2, C89-19.1, L89-5.2, Q89-3.2 (S), R89-27.1
unnamed: C89-20.1, R89-28.1
unnamed: C89-20.2, C89-21.1, L89-4.1, R89-29.1, R89-30.2
unnamed: C89-22.1, L89-4.2, Q89-4.3 (C)
unnamed: C89-23.1, L89-99.1, R89-29.2, R89-36.2
unnamed: C89-24.1, Q89-4.2 (B), R89-30.1, R89-31.2
unnamed: C89-24.2, C89-32.2, C89-33.2, C89-34.1, Q89-5.1 (E), R89-35.2
unnamed: C89-25.1, L89-100.1, R89-36.1
unnamed: C89-26.1, Q89-5.2 (B), R89-33.1, R89-34.2
unnamed: C89-27.1, R89-22.2, R89-22.3, R89-23.1, R89-24.2, R89-38.2
unnamed: C89-29.1, D89-3.1 (K), R89-38.1
unnamed: C89-29.2, C89-31.2, C89-32.1
unnamed: C89-30.1, D89-2.1 (K), R89-39.1
unnamed: C89-30.2, C89-33.1, C89-35.1, L89-1.1
unnamed: C89-31.1, L89-100.2, Q89-5.3 (C), R89-33.2
unnamed: L89-1.2, L89-2.1, L89-3.1
unnamed: L89-103.1, R89-3.2, R89-9.1, R89-10.1, R89-13.1, R89-14.2, R89-16.1, R89-18.1
unnamed: Q89-1.2 (S), Q89-2.2 (B), R89-19.1
unnamed: Q89-4.1 (E), R89-32.2
unnamed: R89-1.2, R89-2.3
unnamed: R89-2.1, R89-3.1
unnamed: R89-4.2, R89-6.2, U89-1.1 (Signal_Input)
unnamed: R89-7.1, U89-1.2 (Gain_Adjust)
unnamed: R89-7.2, U89-1.3 (Gain_Adjust)
unnamed: R89-10.2, U89-1.5 (Bias)
unnamed: R89-8.1, R89-9.2, R89-11.1, R89-12.2, U89-1.8 (Input_Carrier)
unnamed: R89-13.2, U89-1.12 (Output)
unnamed: R89-22.1, S89-1.10 (B4), S89-1.11 (B5)
unnamed: R89-24.1, S89-1.7 (B1), S89-1.8 (B2), S89-1.9 (B3)
unnamed: R89-6.1, R89-28.2, S89-1.21 (D3)
unnamed: S89-1.1 (A1), Y89-1.2
unnamed: S89-1.2 (A2), Y89-2.2
unnamed: S89-1.4 (A4), Y89-3.2
OFFSET: C89-28.1, R89-39.2, V89-3.1
OUT: R89-21.2, R89-89.1
S5: S89-1.5 (A5)

Notes on the sheet:
RFC
S/A 80278
OSC CIRCUIT BD S/A 80277
C10-C12 5-60p
* VFO magnetic, trimmer, and alignment-control values below are inferred simulation-aligned values, not factory specifications .param PTO_L1=0.8u .param PTO_L2=10u .param PTO_L3=13u .param VFO_R2_POS=0.760 .param VFO_R27_POS=0.100 .param VFO_T1_L1=5.221u .param VFO_T1_L2=4.567u .param VFO_T1_K=0.24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
