dmsmccann/triton-540/triton_540.kicad_sch

## KiCad design triton_540.kicad_sch (2026-09-05, an earlier design)

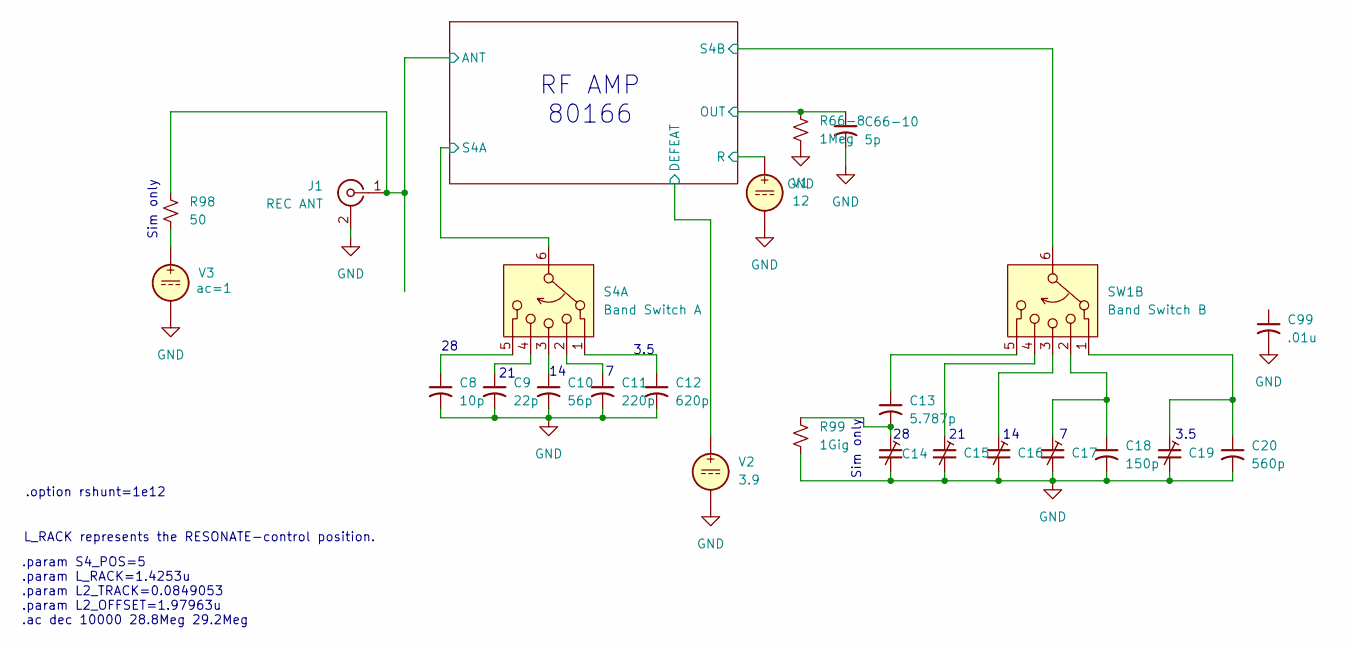
[picture p47: schematic triton_540.kicad_sch]

Parts:
C8: 10p
C9: 22p
C10: 56p
C11: 220p
C12: 620p
C13: 5.787p
C14, C15, C16, C17, C19: 5-60p
C18: 150p
C20: 560p
C66-10: 5p
C99: .01u
J1: REC ANT
R66-8: 1Meg
R98: 50
R99: 1Gig
S4: Band Switch A
SW1: Band Switch B
V1: 12
V2: 3.9
V3: 0

Connections:
ANT: J1.1 (In), R98.2
DEFEAT: V2.1
GND: C8.2, C9.2, C10.2, C11.2, C12.2, C14.2, C15.2, C16.2, C17.2, C18.2, C19.2, C20.2, C66-10.2, C99.2, J1.2 (Ext), R66-8.1, R99.2, V1.2, V2.2, V3.2
unnamed: C8.1, S4.5
unnamed: C9.1, S4.4
unnamed: C10.1, S4.3
unnamed: C11.1, S4.2
unnamed: C12.1, S4.1
unnamed: C13.1, SW1.5
unnamed: C13.2, C14.1, R99.1
unnamed: C15.1, SW1.4
unnamed: C16.1, SW1.3
unnamed: C17.1, C18.1, SW1.2
unnamed: C19.1, C20.1, SW1.1
unnamed: R98.1, V3.1
OUT: C66-10.1, R66-8.2
R: V1.1
S4A: S4.6
S4B: SW1.6

Notes on the sheet:
L_RACK represents the RESONATE-control position.
.param S4_POS=5 .param L_RACK=1.4253u .param L2_TRACK=0.0849053 .param L2_OFFSET=1.97963u .ac dec 10000 28.8Meg 29.2Meg
Sim only
3.5
.option rshunt=1e12
RF AMP 80166
